LarryMorris1964/SmartBlaster/hardware/Reference images/Camera/71ONhgsGphL._AC_SL1500_.jpg

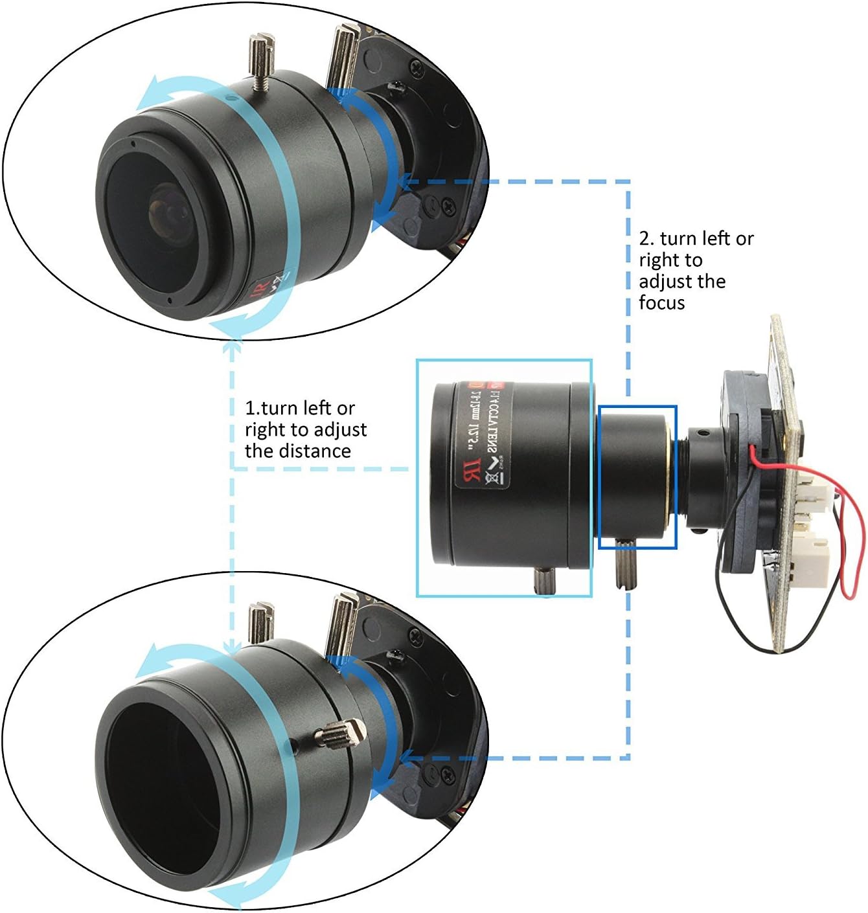
hardware/Reference images/Camera/71ONhgsGphL._AC_SL1500_.jpg
