LarryMorris1964/SmartBlaster/hardware/Reference images/Pi3/Pi3 Connnector Layout.jpg

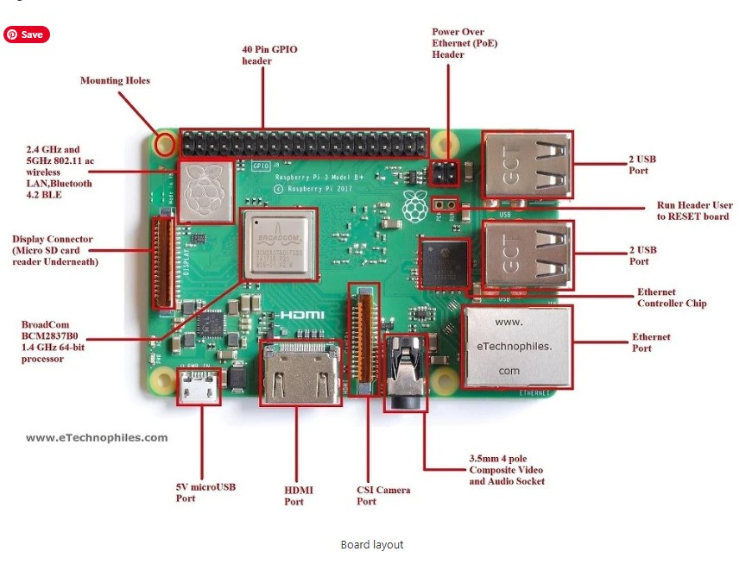
hardware/Reference images/Pi3/Pi3 Connnector Layout.jpg
