LarryMorris1964/SmartBlaster/software/data/samples/midea/sample_001.jpg

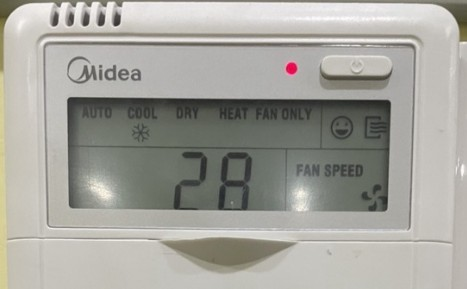
software/data/samples/midea/sample_001.jpg
