LarryMorris1964/SmartBlaster/software/data/samples/midea/sample_002.jpg

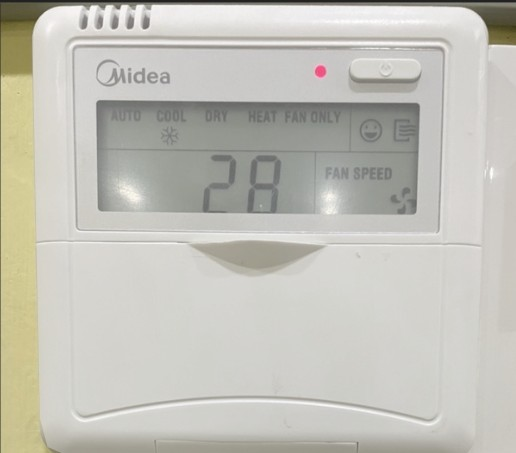
software/data/samples/midea/sample_002.jpg
