LarryMorris1964/SmartBlaster/software/data/samples/midea/sample_003.jpg

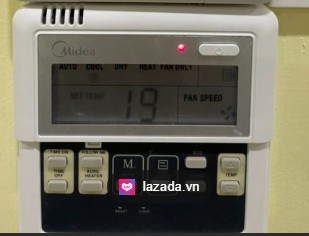
software/data/samples/midea/sample_003.jpg
